calbasantana/rover-challenges-arena/Challenge 6: Welcome to Seattle/3D Prints/Challenge 6 and 7 Ramp Support 2.stl

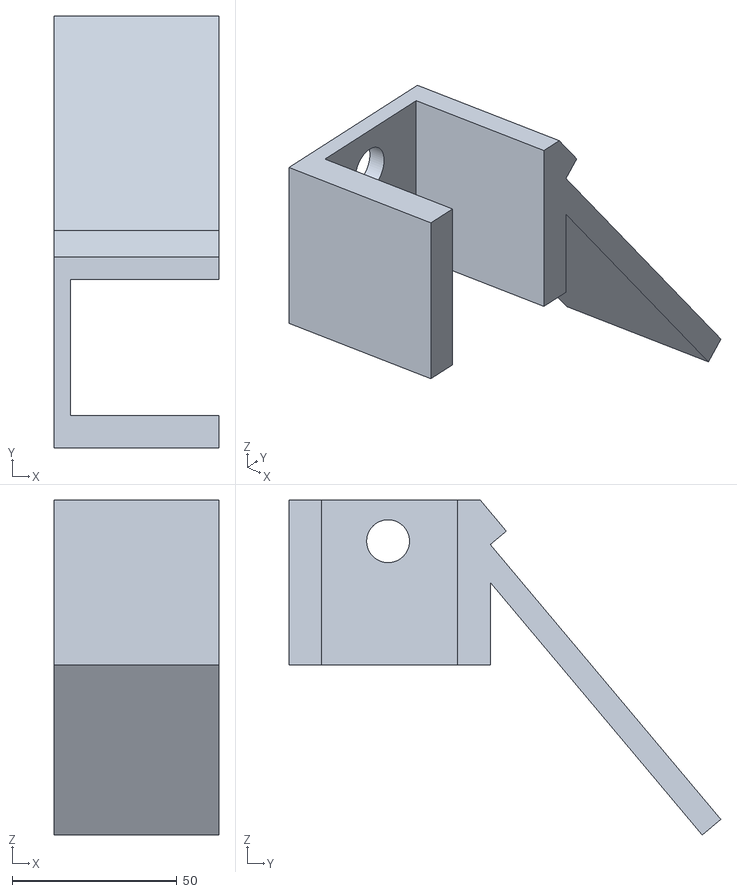
[picture p28: CAD file, 2025-05-12]
Challenge 6: Welcome to Seattle/3D Prints/Challenge 6 and 7 Ramp Support 2.stl
50.0 x 130.9 x 101.6
