calbasantana/rover-challenges-arena/Challenge 6: Welcome to Seattle/Stencils/Challenge 6 and 7 Stencil Top.dxf

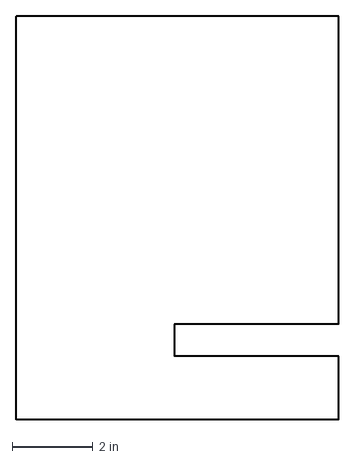
[picture p29: CAD file, 2025-04-30]
Challenge 6: Welcome to Seattle/Stencils/Challenge 6 and 7 Stencil Top.dxf
8.00 x 10.0 in
