calbasantana/rover-challenges-arena/Challenge 7: Down the Canyon/3D Prints/Challenge 7 Tag Back Support.stl

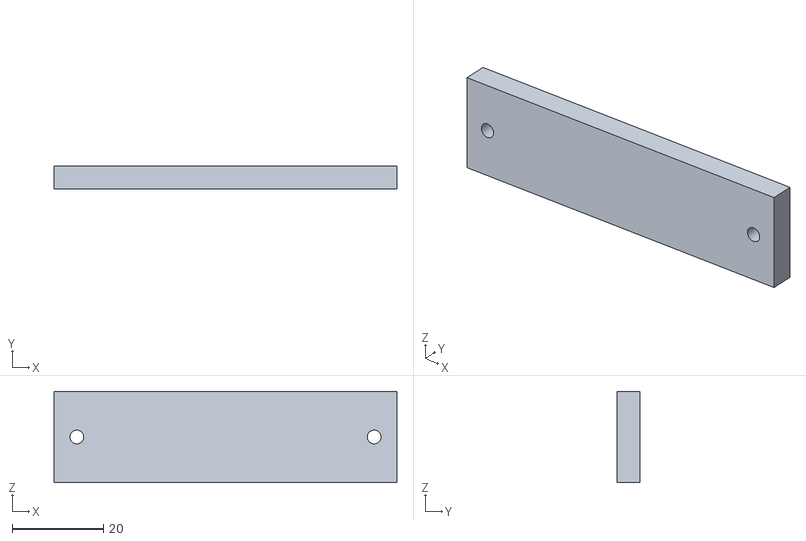
[picture p30: CAD file, 2025-04-30]
Challenge 7: Down the Canyon/3D Prints/Challenge 7 Tag Back Support.stl
75.0 x 5.00 x 20.0
