calbasantana/rover-challenges-arena/Challenge 8: Giving a Gift/3D Prints/Challenge 8 Tag.stl

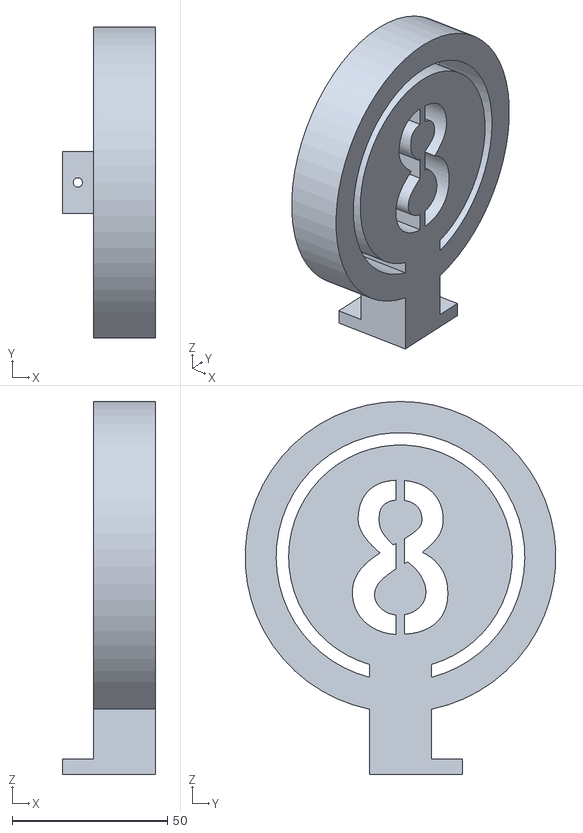
[picture p31: CAD file, 2025-04-30]
Challenge 8: Giving a Gift/3D Prints/Challenge 8 Tag.stl
30.0 x 99.9 x 120.0
