calbasantana/rover-challenges-arena/Challenge 9: SUMO/3D Prints/Challenge 9 Top Support 11.stl

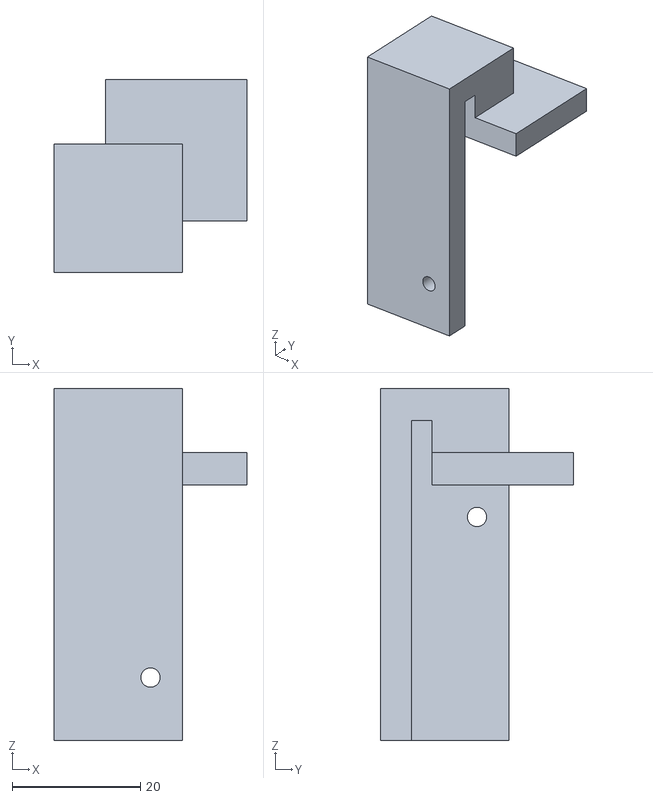
[picture p33: CAD file, 2025-04-30]
Challenge 9: SUMO/3D Prints/Challenge 9 Top Support 11.stl
30.0 x 30.0 x 54.8
