calbasantana/rover-challenges-arena/Challenge 10: Resupply Mission/3D Prints/Challenge 10 Tag Attachment.stl

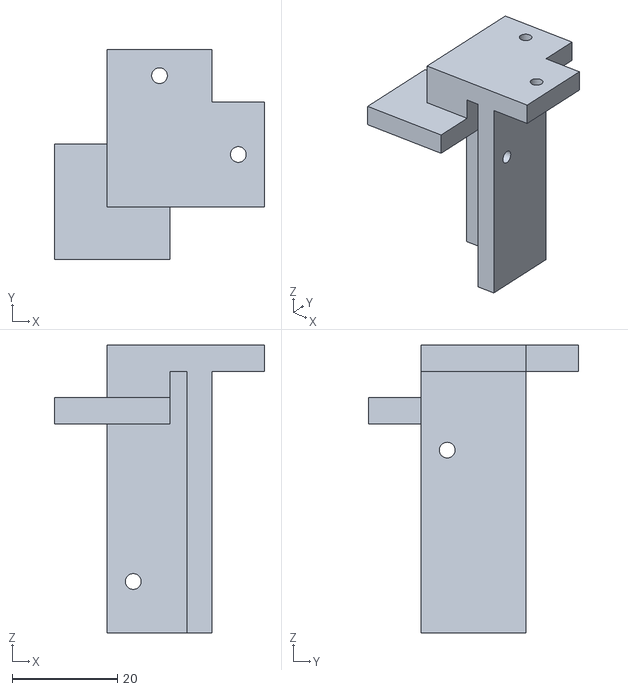
[picture p35: CAD file, 2025-04-30]
Challenge 10: Resupply Mission/3D Prints/Challenge 10 Tag Attachment.stl
40.0 x 40.0 x 54.8
