calbasantana/rover-challenges-arena/Challenge 10: Resupply Mission/Stencils/Challenge 10 Start Stencil.dxf

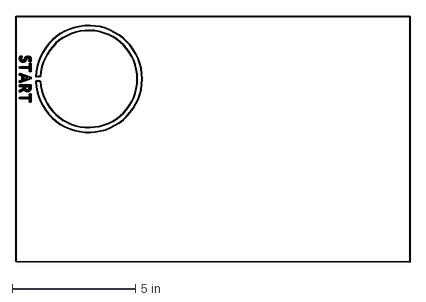
[picture p36: CAD file, 2025-04-30]
Challenge 10: Resupply Mission/Stencils/Challenge 10 Start Stencil.dxf
16.0 x 10.00 in
