calbasantana/rover-challenges-arena/Challenge 1: Hercules's Push/Stencils/Challenge 1 Start Stencil.dxf

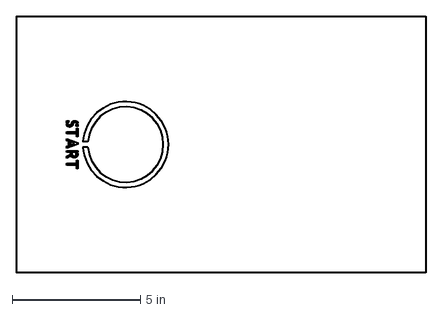
[picture p37: CAD file, 2025-04-29]
Challenge 1: Hercules's Push/Stencils/Challenge 1 Start Stencil.dxf
16.0 x 10.0 in
