calbasantana/rover-challenges-arena/Challenge 2: How Far?/3D Prints/Challenge 2 Side Support (X6).stl

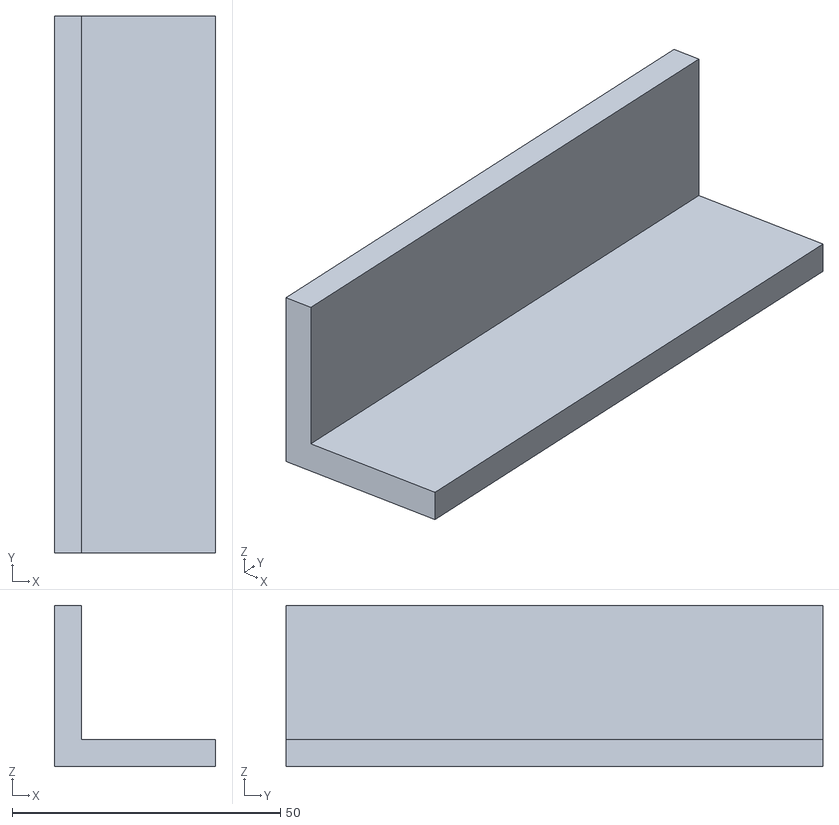
[picture p38: CAD file, 2025-04-29]
Challenge 2: How Far?/3D Prints/Challenge 2 Side Support (X6).stl
30.0 x 100.0 x 30.0
