calbasantana/rover-challenges-arena/Challenge 2: How Far?/Laser Cuts/Challenge 2 Wall 12.dxf

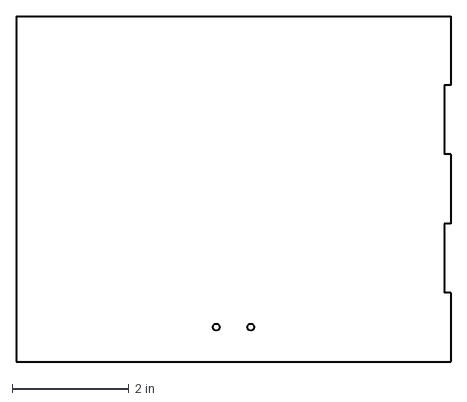
[picture p39: CAD file, 2025-04-29]
Challenge 2: How Far?/Laser Cuts/Challenge 2 Wall 12.dxf
7.44 x 5.91 in
