calbasantana/rover-challenges-arena/Challenge 2: How Far?/Stencils/Challenge 2 Stencil Support 1.dxf

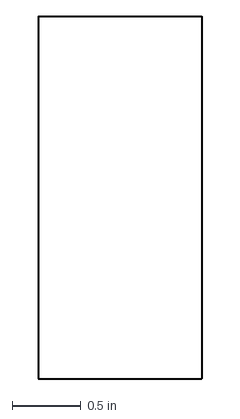
[picture p40: CAD file, 2025-04-29]
Challenge 2: How Far?/Stencils/Challenge 2 Stencil Support 1.dxf
1.19 x 2.64 in
