calbasantana/rover-challenges-arena/Challenge 3: A Rocky Landing/3D Prints/Challenge 3 Bottom Support 2.stl

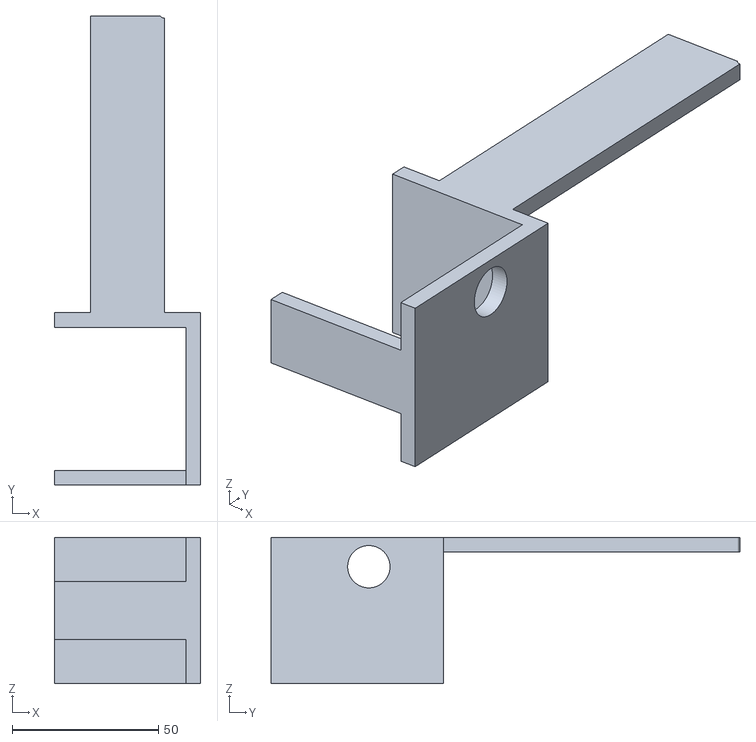
[picture p41: CAD file, 2025-04-29]
Challenge 3: A Rocky Landing/3D Prints/Challenge 3 Bottom Support 2.stl
50.0 x 160.6 x 50.0
