calbasantana/rover-challenges-arena/Challenge 3: A Rocky Landing/Stencils/Challenge 3 End Stencil.dxf

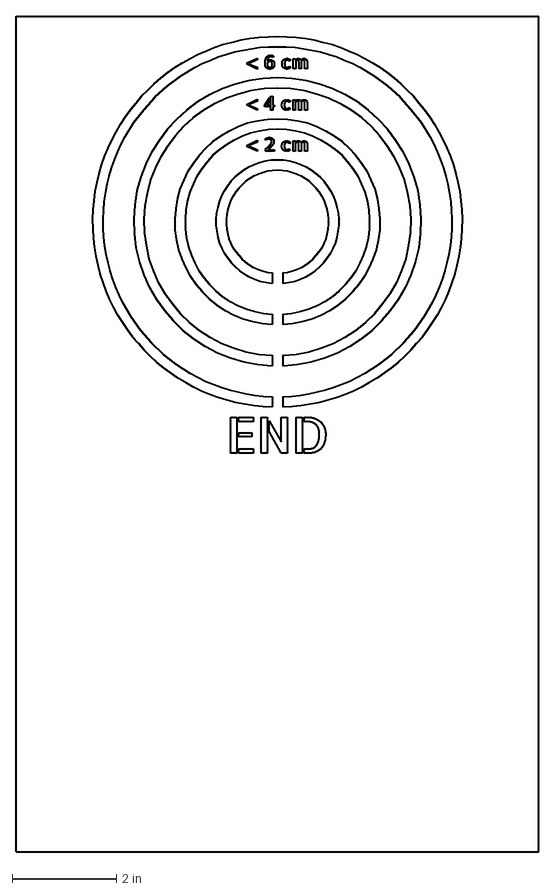
[picture p42: CAD file, 2025-04-29]
Challenge 3: A Rocky Landing/Stencils/Challenge 3 End Stencil.dxf
10.0 x 16.0 in
