calbasantana/rover-challenges-arena/Challenge 4: A Way Out/3D Prints/Challenge 4 Tag.stl

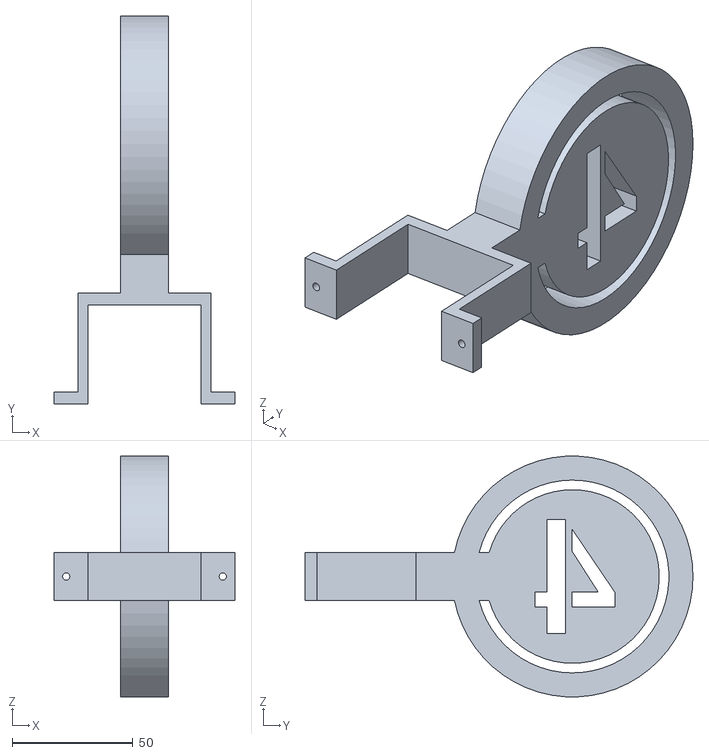
[picture p43: CAD file, 2025-04-29]
Challenge 4: A Way Out/3D Prints/Challenge 4 Tag.stl
75.0 x 161.0 x 99.9
