calbasantana/rover-challenges-arena/Challenge 4: A Way Out/Laser Cuts/Challenge 4 Maze Center Piece.dxf

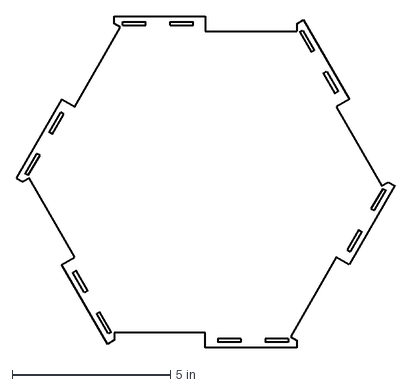
[picture p44: CAD file, 2025-04-29]
Challenge 4: A Way Out/Laser Cuts/Challenge 4 Maze Center Piece.dxf
12.0 x 10.5 in
