calbasantana/rover-challenges-arena/Challenge 5: Surface Navigation/Laser Cuts/Challenge 5 Wall 10.dxf

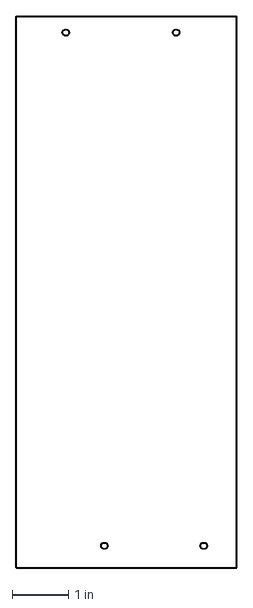
[picture p45: CAD file, 2025-04-30]
Challenge 5: Surface Navigation/Laser Cuts/Challenge 5 Wall 10.dxf
3.94 x 9.84 in
