calbasantana/rover-challenges-arena/Challenge 8: Giving a Gift/3D Prints/Challenge 8 Team B Flag.stl

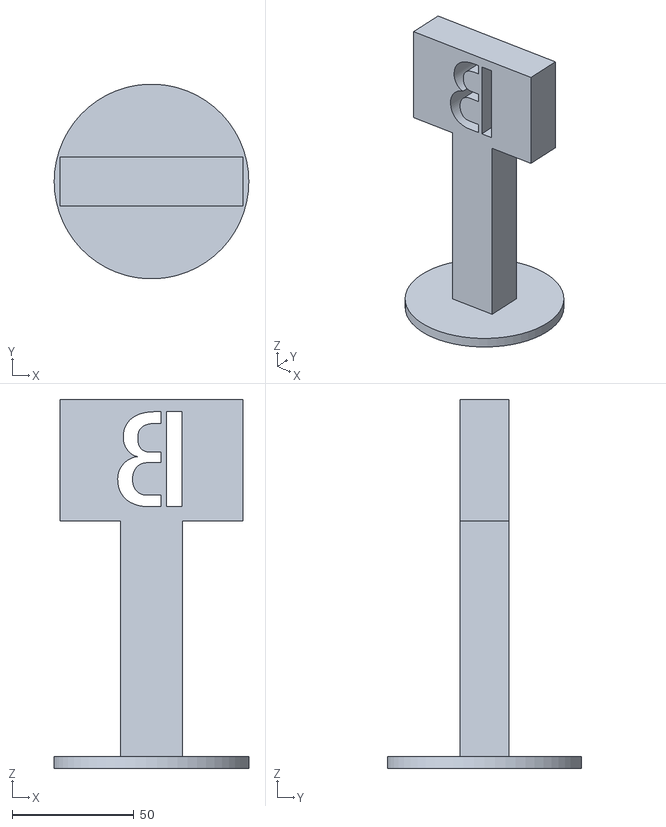
[picture p46: CAD file, 2025-04-30]
Challenge 8: Giving a Gift/3D Prints/Challenge 8 Team B Flag.stl
80.0 x 79.9 x 151.6
