calbasantana/rover-challenges-arena/Challenge 8: Giving a Gift/Stencils/Challenge 8 Team B Stencil.dxf

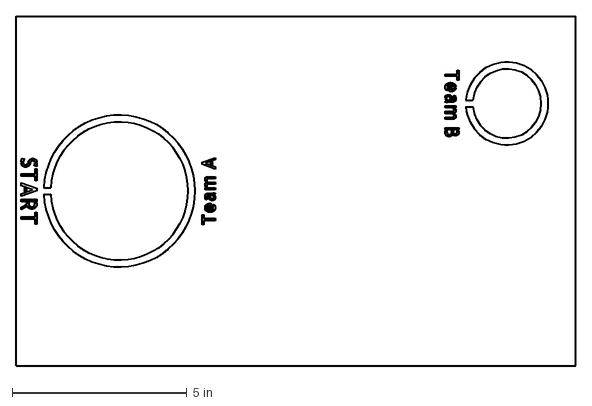
[picture p47: CAD file, 2025-04-30]
Challenge 8: Giving a Gift/Stencils/Challenge 8 Team B Stencil.dxf
16.0 x 10.0 in
