calbasantana/rover-challenges-arena/Challenge 9: SUMO/Laser Cuts/Challenge 9 SUMO Piece 15.dxf

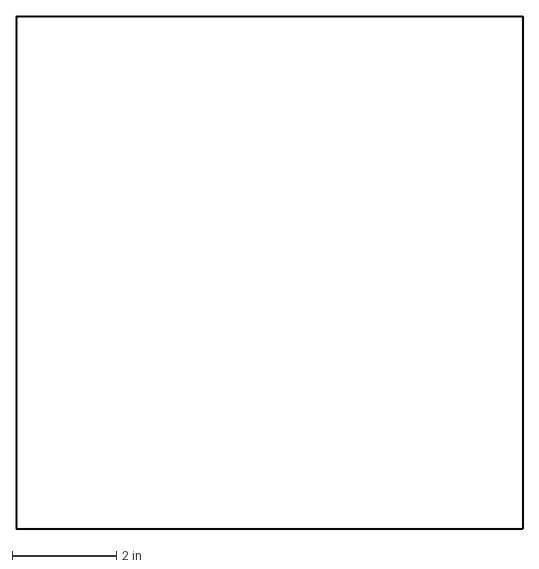
[picture p48: CAD file, 2025-04-30]
Challenge 9: SUMO/Laser Cuts/Challenge 9 SUMO Piece 15.dxf
9.72 x 9.84 in
