calbasantana/rover-challenges-arena/Challenge 10: Resupply Mission/3D Prints/Challenge 10 Tag.stl

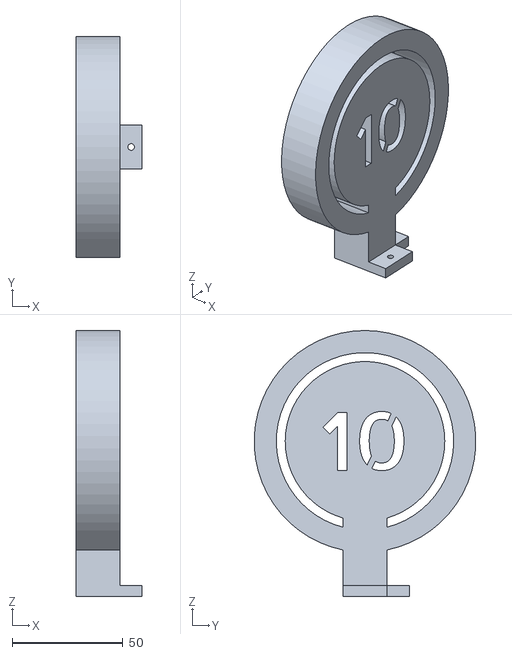
[picture p49: CAD file, 2025-04-30]
Challenge 10: Resupply Mission/3D Prints/Challenge 10 Tag.stl
30.0 x 99.9 x 120.0
