calbasantana/rover-challenges-arena/Challenge 10: Resupply Mission/Stencils/Challenge 10 End Stencil.dxf

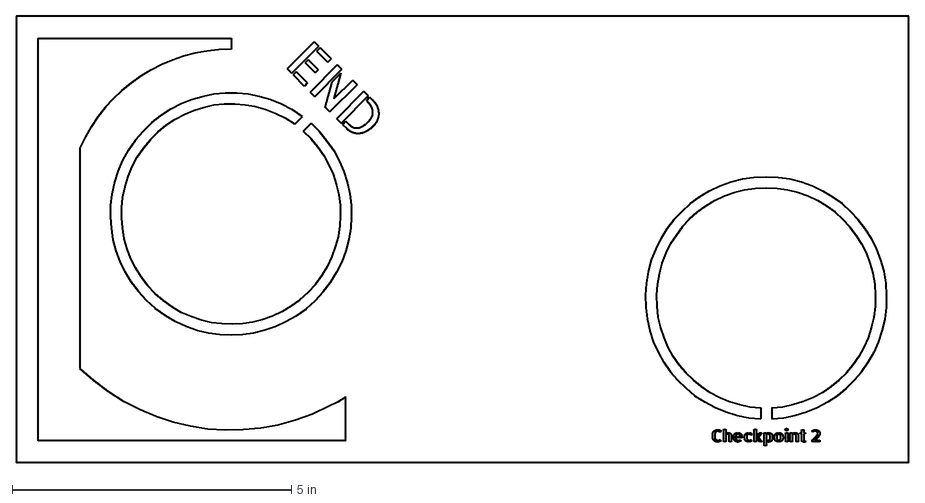
[picture p50: CAD file, 2025-04-30]
Challenge 10: Resupply Mission/Stencils/Challenge 10 End Stencil.dxf
16.0 x 8.00 in
