calbasantana/rover-challenges-arena/Challenge 1: Hercules's Push/3D Prints/Challenge 1 Tag.stl

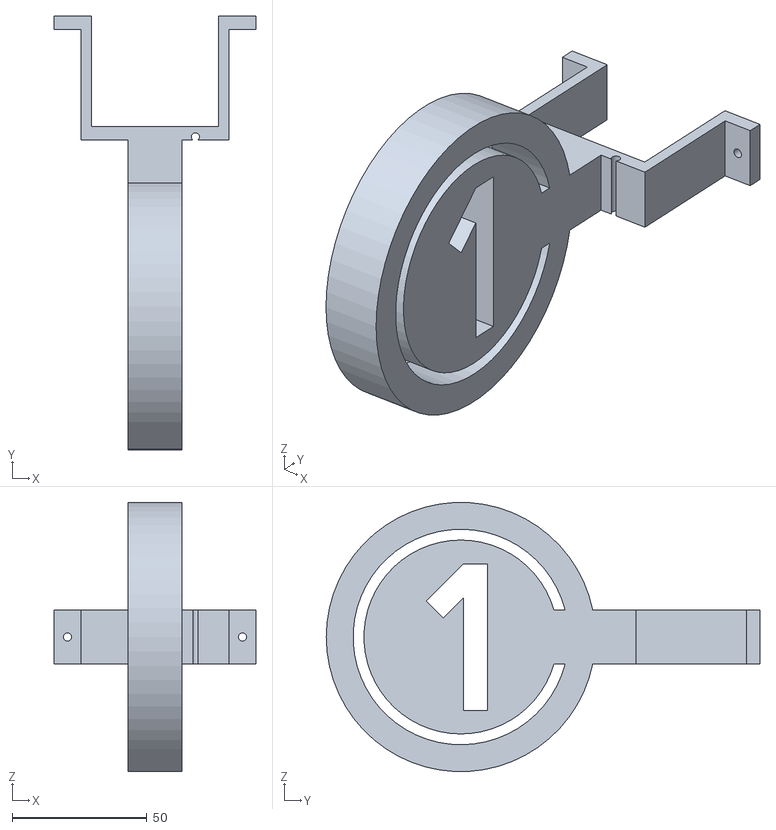
[picture p51: CAD file, 2025-04-29]
Challenge 1: Hercules's Push/3D Prints/Challenge 1 Tag.stl
75.0 x 161.0 x 99.9
