calbasantana/rover-challenges-arena/Challenge 2: How Far?/Laser Cuts/Challenge 2 Wall 10.dxf

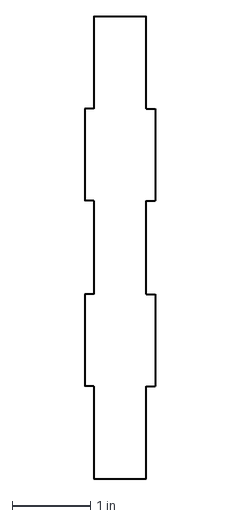
[picture p53: CAD file, 2025-04-29]
Challenge 2: How Far?/Laser Cuts/Challenge 2 Wall 10.dxf
0.906 x 5.91 in
