calbasantana/rover-challenges-arena/Challenge 2: How Far?/Stencils/Challenge 2 Stencil Support 2.dxf

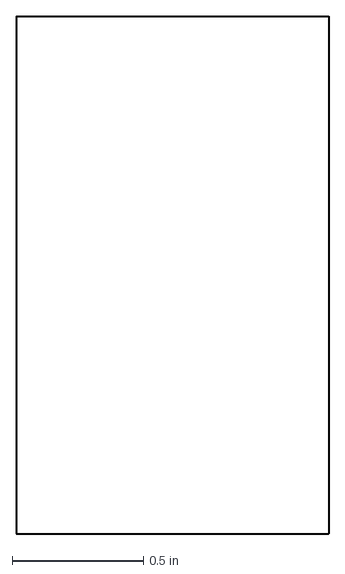
[picture p54: CAD file, 2025-04-29]
Challenge 2: How Far?/Stencils/Challenge 2 Stencil Support 2.dxf
1.19 x 1.97 in
