calbasantana/rover-challenges-arena/Challenge 5: Surface Navigation/3D Prints/Challenge 5 Top Support 5.stl

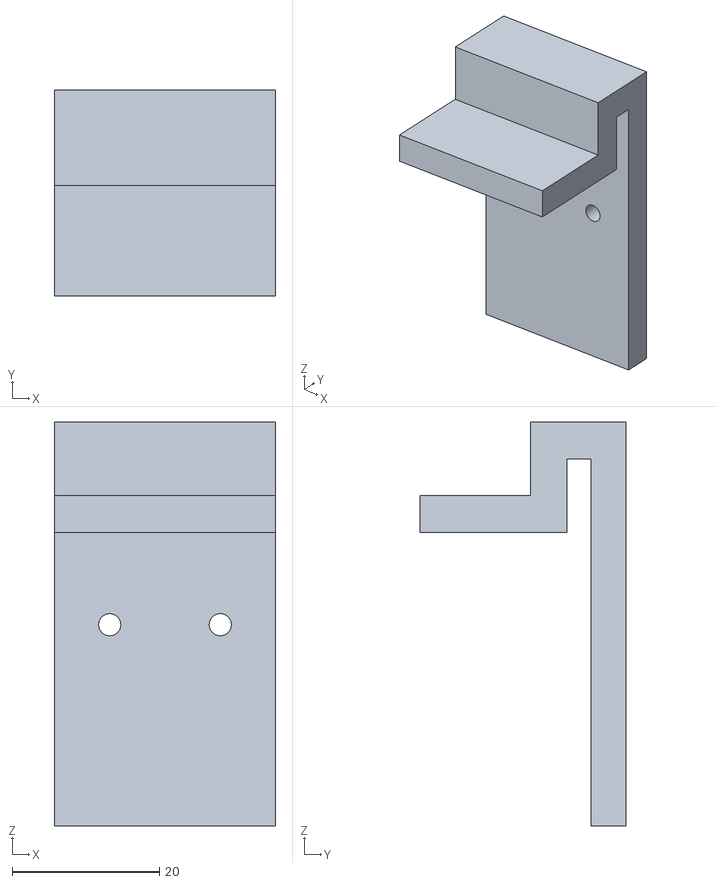
[picture p55: CAD file, 2025-04-30]
Challenge 5: Surface Navigation/3D Prints/Challenge 5 Top Support 5.stl
30.0 x 28.0 x 54.8
