calbasantana/rover-challenges-arena/Challenge 5: Surface Navigation/Laser Cuts/Challenge 5 Wall 8.dxf

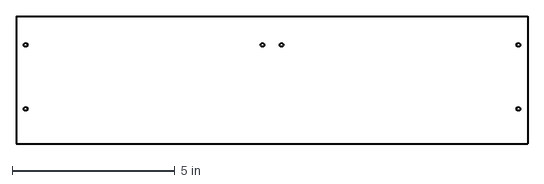
[picture p56: CAD file, 2025-04-30]
Challenge 5: Surface Navigation/Laser Cuts/Challenge 5 Wall 8.dxf
15.7 x 3.94 in
