calbasantana/rover-challenges-arena/Challenge 9: SUMO/Laser Cuts/Challenge 9 Wall 9.dxf

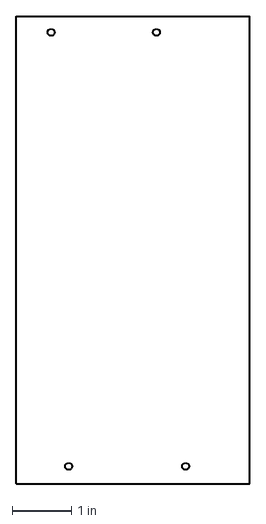
[picture p57: CAD file, 2025-04-30]
Challenge 9: SUMO/Laser Cuts/Challenge 9 Wall 9.dxf
3.94 x 7.87 in
