calbasantana/rover-challenges-arena/Challenge 2: How Far?/3D Prints/Challenge 2 Bottom Support 2.stl

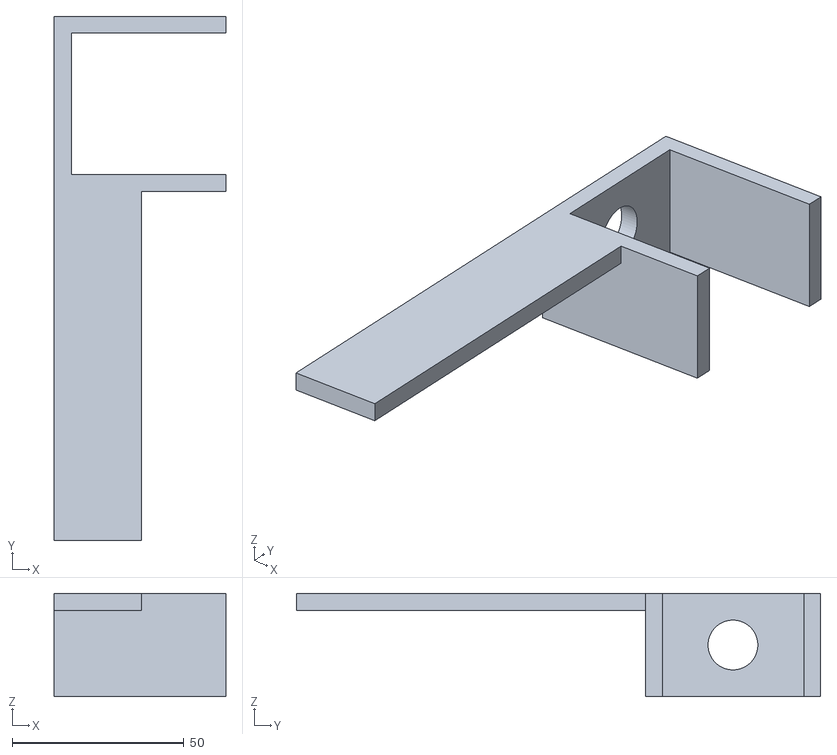
[picture p58: CAD file, 2025-04-29]
Challenge 2: How Far?/3D Prints/Challenge 2 Bottom Support 2.stl
50.0 x 152.6 x 30.0
