calbasantana/rover-challenges-arena/Challenge 2: How Far?/Laser Cuts/Challenge 2 Wall 8.dxf

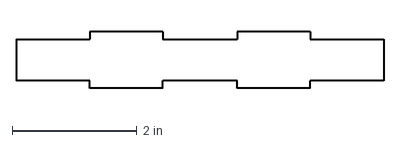
[picture p59: CAD file, 2025-04-29]
Challenge 2: How Far?/Laser Cuts/Challenge 2 Wall 8.dxf
5.91 x 0.906 in
