calbasantana/rover-challenges-arena/Challenge 5: Surface Navigation/Laser Cuts/Challenge 5 Wall 5.dxf

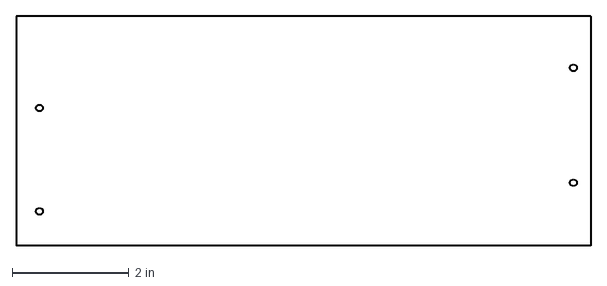
[picture p60: CAD file, 2025-04-30]
Challenge 5: Surface Navigation/Laser Cuts/Challenge 5 Wall 5.dxf
9.84 x 3.94 in
