calbasantana/rover-challenges-arena/Challenge 9: SUMO/Laser Cuts/Challenge 9 SUMO Piece 9.dxf

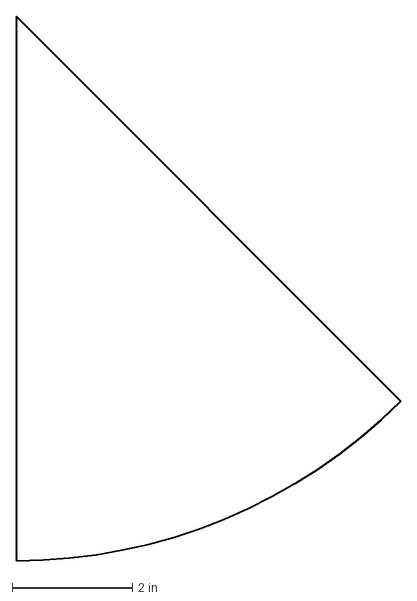
[picture p62: CAD file, 2025-04-30]
Challenge 9: SUMO/Laser Cuts/Challenge 9 SUMO Piece 9.dxf
6.40 x 9.06 in
