calbasantana/rover-challenges-arena/Challenge 2: How Far?/Laser Cuts/Challenge 2 Wall 1.dxf

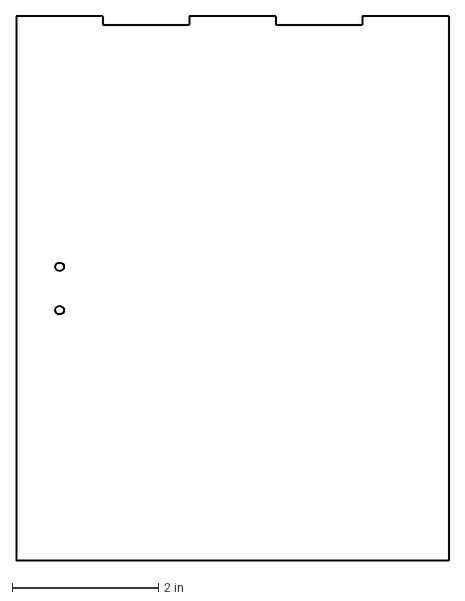
[picture p63: CAD file, 2025-04-29]
Challenge 2: How Far?/Laser Cuts/Challenge 2 Wall 1.dxf
5.91 x 7.44 in
