calbasantana/rover-challenges-arena/Challenge 5: Surface Navigation/3D Prints/Challenge 5 Bottom Support 4.stl

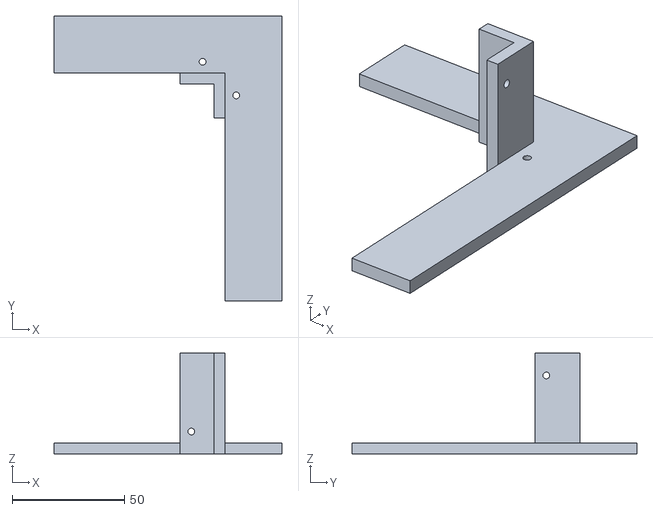
[picture p64: CAD file, 2025-04-30]
Challenge 5: Surface Navigation/3D Prints/Challenge 5 Bottom Support 4.stl
101.6 x 127.0 x 45.0
