calbasantana/rover-challenges-arena/Challenge 5: Surface Navigation/Laser Cuts/Challenge 5 Wall 2.dxf

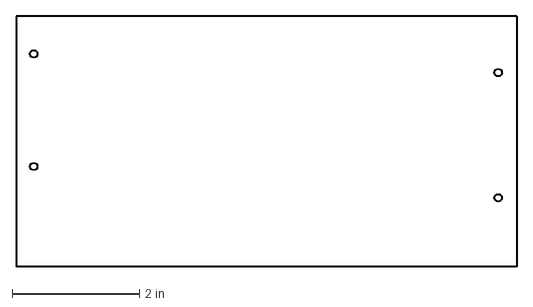
[picture p65: CAD file, 2025-04-30]
Challenge 5: Surface Navigation/Laser Cuts/Challenge 5 Wall 2.dxf
7.87 x 3.94 in
