calbasantana/rover-challenges-arena/Challenge 9: SUMO/Laser Cuts/Challenge 9 Wall 10.dxf

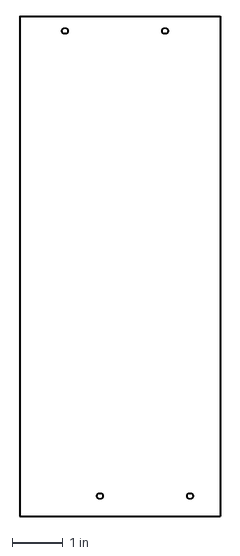
[picture p66: CAD file, 2025-04-30]
Challenge 9: SUMO/Laser Cuts/Challenge 9 Wall 10.dxf
3.94 x 9.84 in
