calbasantana/rover-challenges-arena/Challenge 2: How Far?/Laser Cuts/Challenge 2 Wall 11.dxf

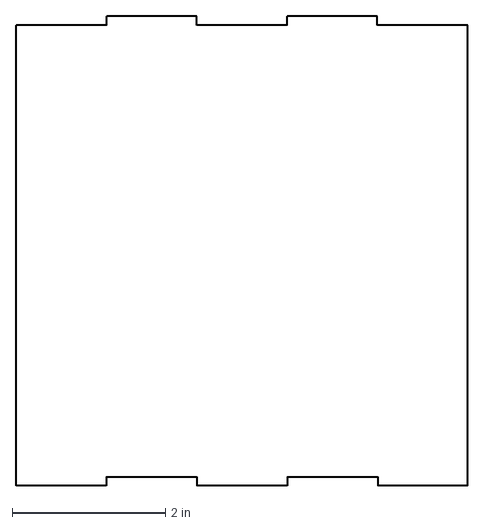
[picture p67: CAD file, 2025-04-29]
Challenge 2: How Far?/Laser Cuts/Challenge 2 Wall 11.dxf
5.91 x 6.14 in
