calbasantana/rover-challenges-arena/Challenge 3: A Rocky Landing/3D Prints/Challenge 3 Tag.stl

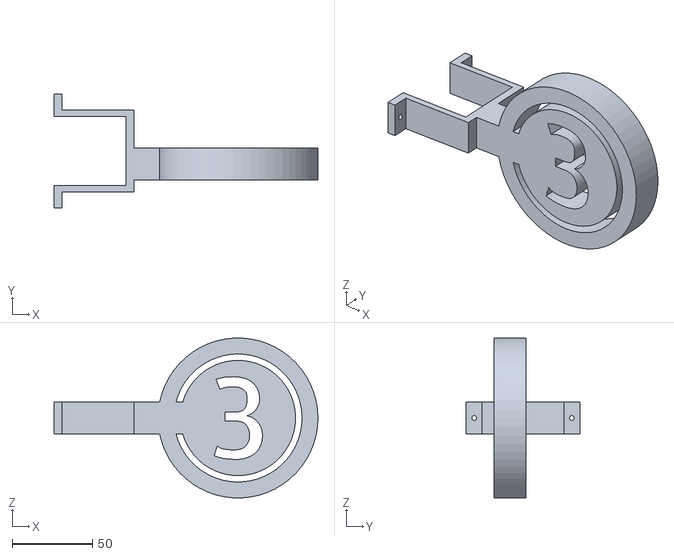
[picture p68: CAD file, 2025-04-29]
Challenge 3: A Rocky Landing/3D Prints/Challenge 3 Tag.stl
165.0 x 71.0 x 99.9
