calbasantana/rover-challenges-arena/Challenge 9: SUMO/Laser Cuts/Challenge 9 Wall 1.dxf

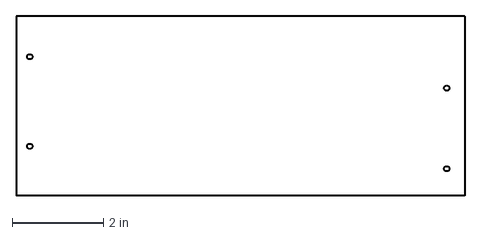
[picture p70: CAD file, 2025-04-30]
Challenge 9: SUMO/Laser Cuts/Challenge 9 Wall 1.dxf
9.84 x 3.94 in
