calbasantana/rover-challenges-arena/Challenge 1: Hercules's Push/3D Prints/Challenge 1 Tag Back Support.stl

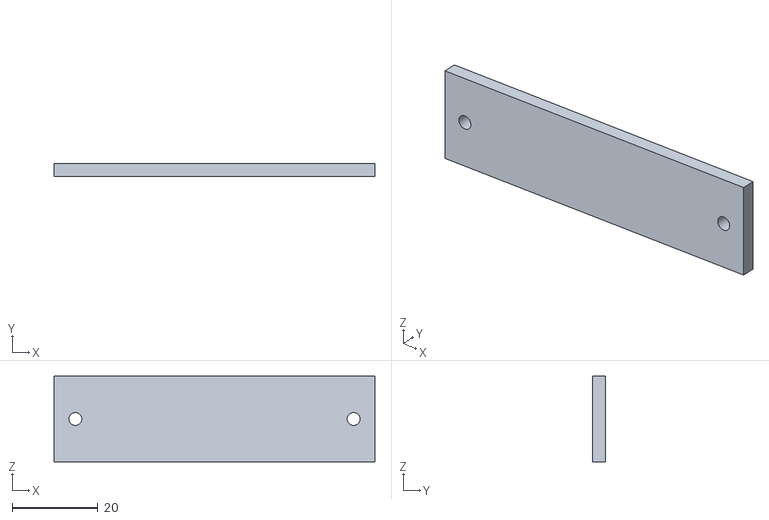
[picture p71: CAD file, 2025-04-29]
Challenge 1: Hercules's Push/3D Prints/Challenge 1 Tag Back Support.stl
75.0 x 3.00 x 20.0
