calbasantana/rover-challenges-arena/Challenge 2: How Far?/3D Prints/Challenge 2 Rope Attachment 1.stl

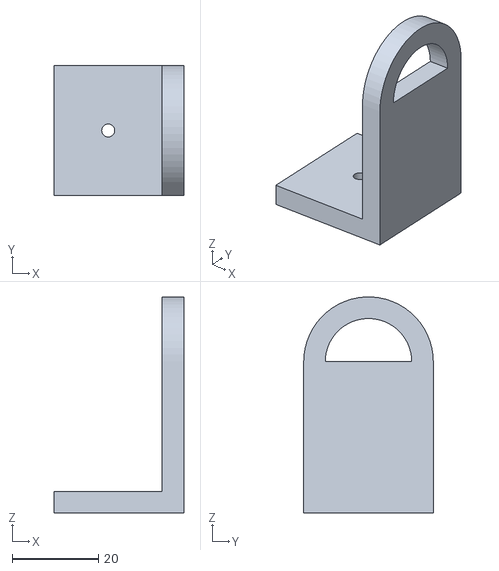
[picture p72: CAD file, 2025-04-29]
Challenge 2: How Far?/3D Prints/Challenge 2 Rope Attachment 1.stl
30.0 x 30.0 x 50.0
