calbasantana/rover-challenges-arena/Challenge 3: A Rocky Landing/3D Prints/Challenge 3 Tag Back Support.stl

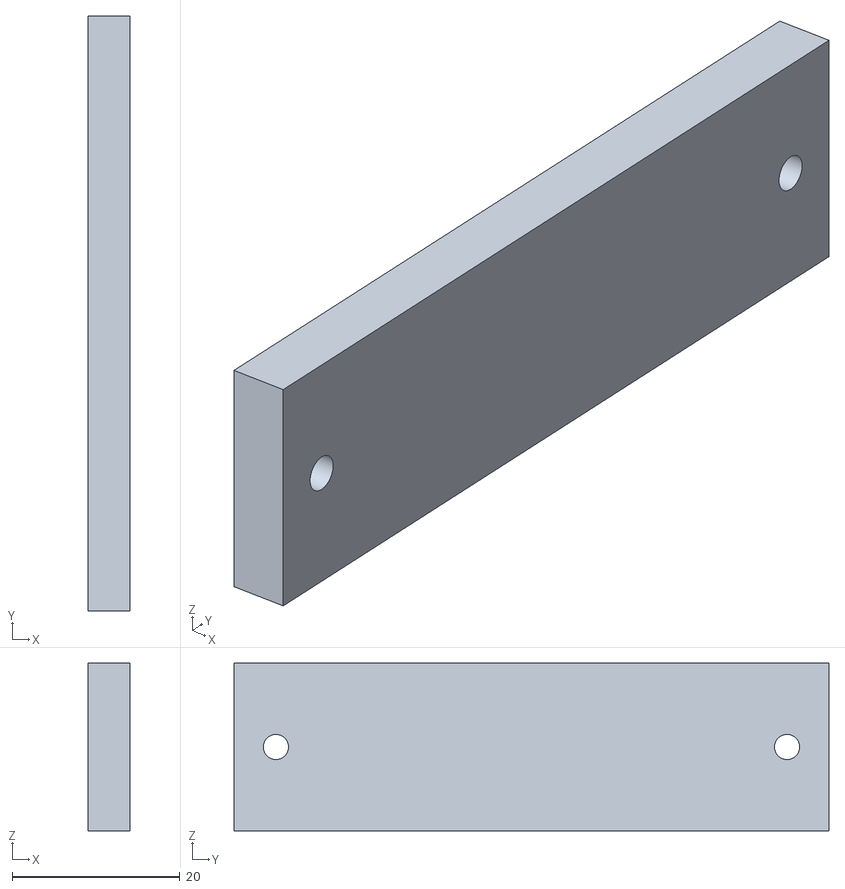
[picture p74: CAD file, 2025-04-29]
Challenge 3: A Rocky Landing/3D Prints/Challenge 3 Tag Back Support.stl
5.00 x 71.0 x 20.0
