calbasantana/rover-challenges-arena/Challenge 9: SUMO/Laser Cuts/Challenge 9 SUMO Piece 7.dxf

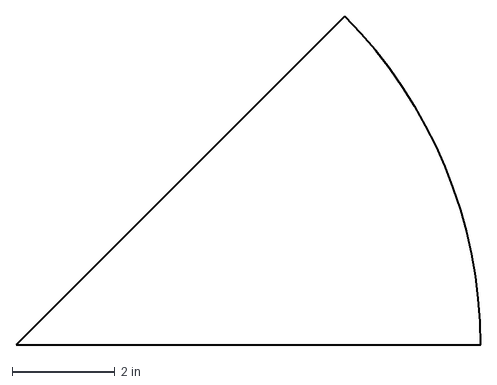
[picture p76: CAD file, 2025-04-30]
Challenge 9: SUMO/Laser Cuts/Challenge 9 SUMO Piece 7.dxf
9.06 x 6.40 in
