calbasantana/rover-challenges-arena/Challenge 9: SUMO/Laser Cuts/Challenge 9 SUMO Piece 11.dxf

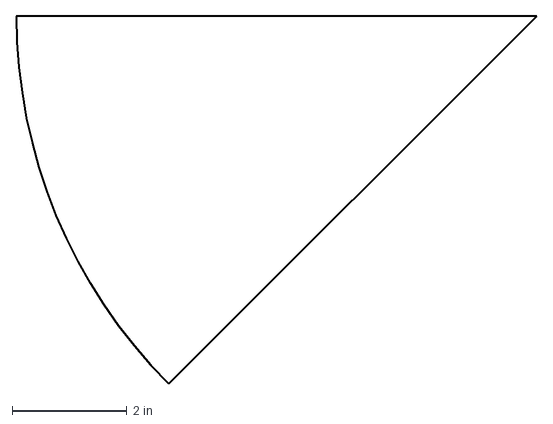
[picture p79: CAD file, 2025-04-30]
Challenge 9: SUMO/Laser Cuts/Challenge 9 SUMO Piece 11.dxf
9.06 x 6.40 in
