calbasantana/rover-challenges-arena/Challenge 9: SUMO/Laser Cuts/Challenge 9 Wall 3.dxf

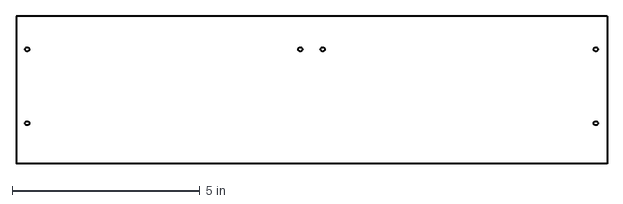
[picture p92: CAD file, 2025-04-30]
Challenge 9: SUMO/Laser Cuts/Challenge 9 Wall 3.dxf
15.7 x 3.94 in
