calbasantana/rover-challenges-arena/Challenge 9: SUMO/Laser Cuts/Challenge 9 Wall 8.dxf

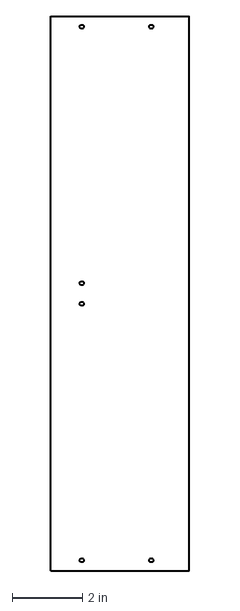
[picture p93: CAD file, 2025-04-30]
Challenge 9: SUMO/Laser Cuts/Challenge 9 Wall 8.dxf
3.94 x 15.7 in
